holmesrichards/vcapf/Simulations/VCAPF_2pole.asc

C1: cap; 100n
C2: cap; 100n
C4: cap; 4.7n
Q1: pnp
Q2: pnp
R1: res; 10k
R2: res; 220
R3: res; 220
R4: res; 10k
R5: res; 10k
R6: res; 220
R7: res; 220
R8: res; 100k
R9: res; 30k
R10: res; 10k
R11: res; 10k
R12: res; 470k
R13: res; 1.8k
R14: res; 100k
R15: res; 4.7k
R16: res; 10k
R17: res; 30k
R18: res; 7.5k
R19: res; 7.5k
R20: res; 100k
R21: res; 30k
R22: res; 15k
R23: res; 10k
R24: res; 30k
R27: res; 10k
U1: TL074
U2: TL074
U3: TL074
U4: TL074
U5: lm13700
U6: TL074
U7: TL074
U8: lm13700
V1: voltage; 12
V2: voltage; -12
V3: voltage; PULSE(-3 3 0 .001u .001u 10m 20m); AC 1 0
V4: voltage; {cv}
V5: voltage; PULSE(-3 3 0 20m .001u 0 20m); AC 1 0
V6: voltage; PULSE(-3 3 0 10m 10m 0 20m); AC 1 0
V7: voltage; PULSE(-3 3 0 .001u .001u 5m 20m); AC 1 0
Named nets: 0, Vp12, Vm12, INPUT_SQUARE, CV, INPUT_PULSE, STAGE1, STAGE2, OUTPUT_2pole, INPUT_RAMP, INPUT_TRI, OUTPUT_1POLE
.include potentiometer.sub
.ac oct 30 .01 1000
;tran 0 100m 60m
;.step param cv 0 5 1
.param cv=0
